w5xd/MK1101/mk1101/pdf/MK1101-lettering.pdf

MK-1101

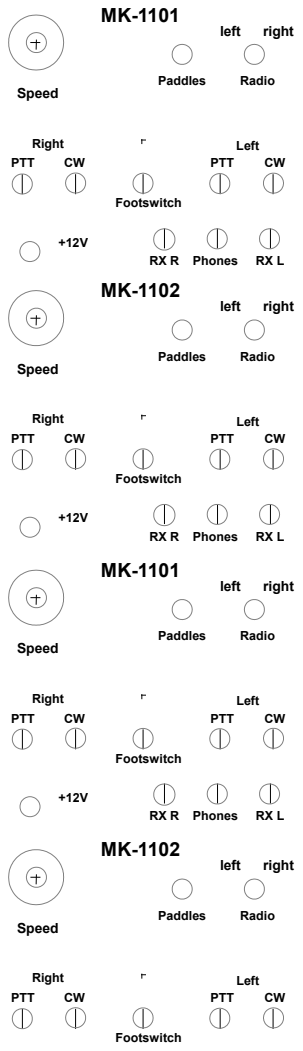
[picture p1: page 1]
Speed; Paddles; Radio; left; right; Right; Left; Footswitch; PTT; RX R Phones
