w5xd/MK1101/mk1103/pcb step/Relay SPDT.stp

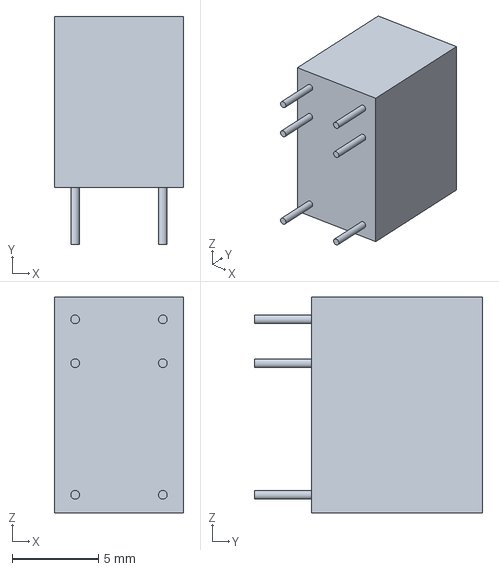
[picture p18: CAD file, 2022-04-01]
mk1103/pcb step/Relay SPDT.stp
7.50 x 13.2 x 12.5 mm
