w5xd/MK1101/mk1103/pcb step/PDB25S564GTLF.stp

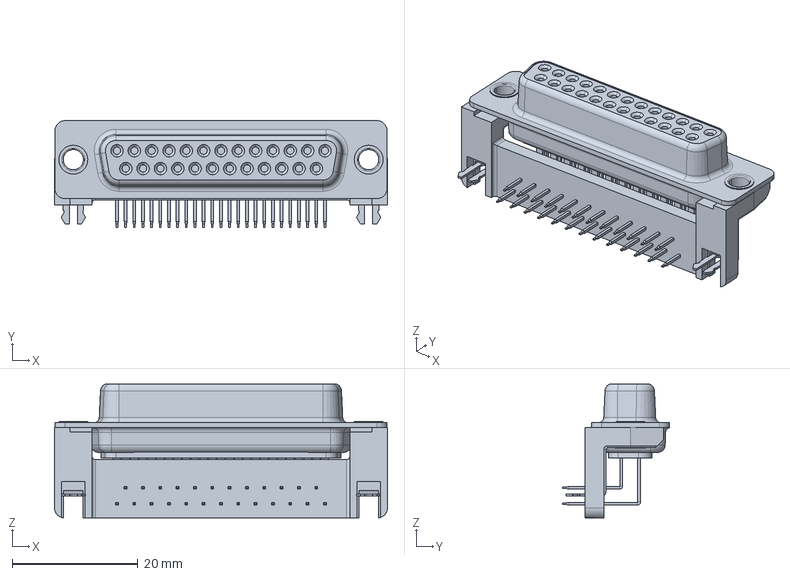
[picture p19: CAD file, 2022-04-01]
mk1103/pcb step/PDB25S564GTLF.stp
53.0 x 17.0 x 21.3 mm
