w5xd/MK1101/mk1103/pcb step/speed pot.stp

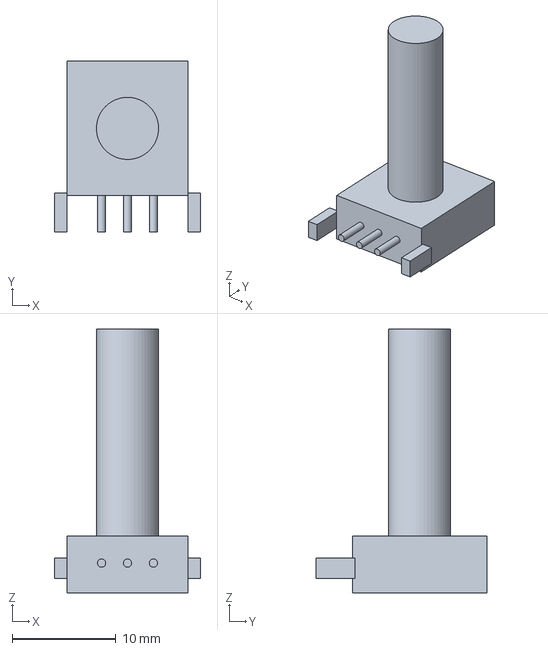
[picture p20: CAD file, 2022-04-01]
mk1103/pcb step/speed pot.stp
14.1 x 16.5 x 25.5 mm
