w5xd/MK1101/mk1103/pcb step/buzzer.stp

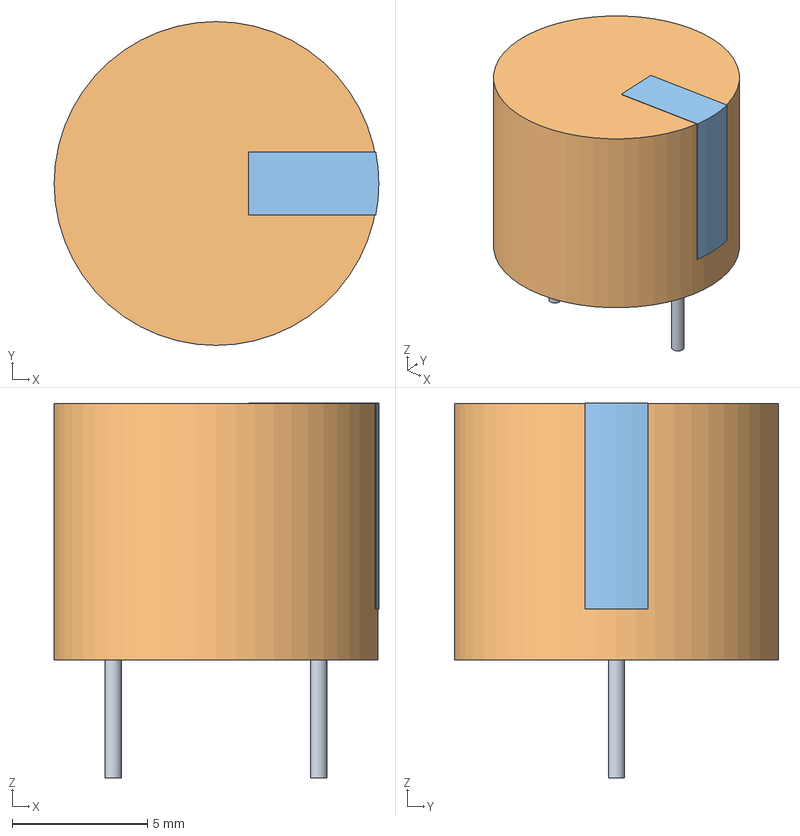
[picture p21: CAD file, 2022-04-01]
mk1103/pcb step/buzzer.stp
12.0 x 12.0 x 13.9 mm
